skiselev/Z80-512K/images/No_CPU_Supervisor-Jumpers.jpg

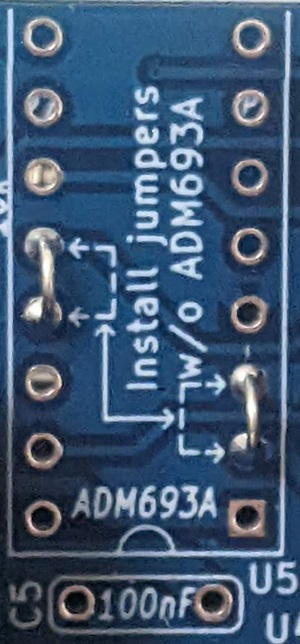
images/No_CPU_Supervisor-Jumpers.jpg
