skiselev/Z80-512K/images/Component-Standoff-Screw.jpg

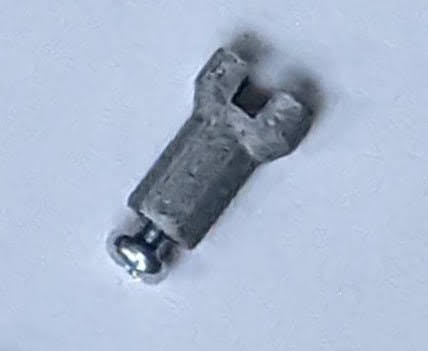
images/Component-Standoff-Screw.jpg
